SolderedElectronics/Soldered-Inkplate-6-hardware-design/OUTPUTS/V1.2.1/333232.jpg

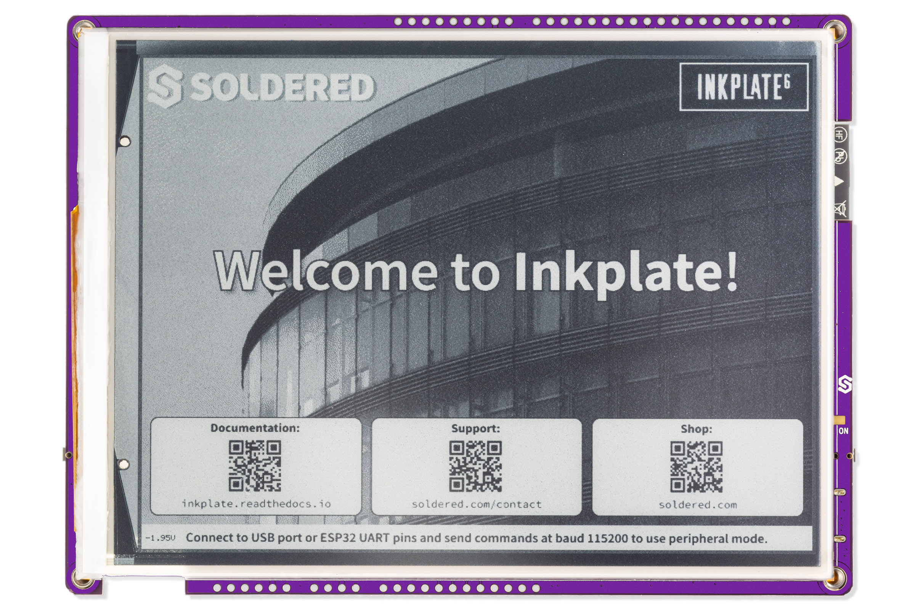
OUTPUTS/V1.2.1/333232.jpg
