SolderedElectronics/Soldered-Inkplate-6-hardware-design/CAD/V1.2.1/CTRL&COMS.kicad_sch

## KiCad design CAD/V1.2.1/CTRL&COMS.kicad_sch (2023-07-25)

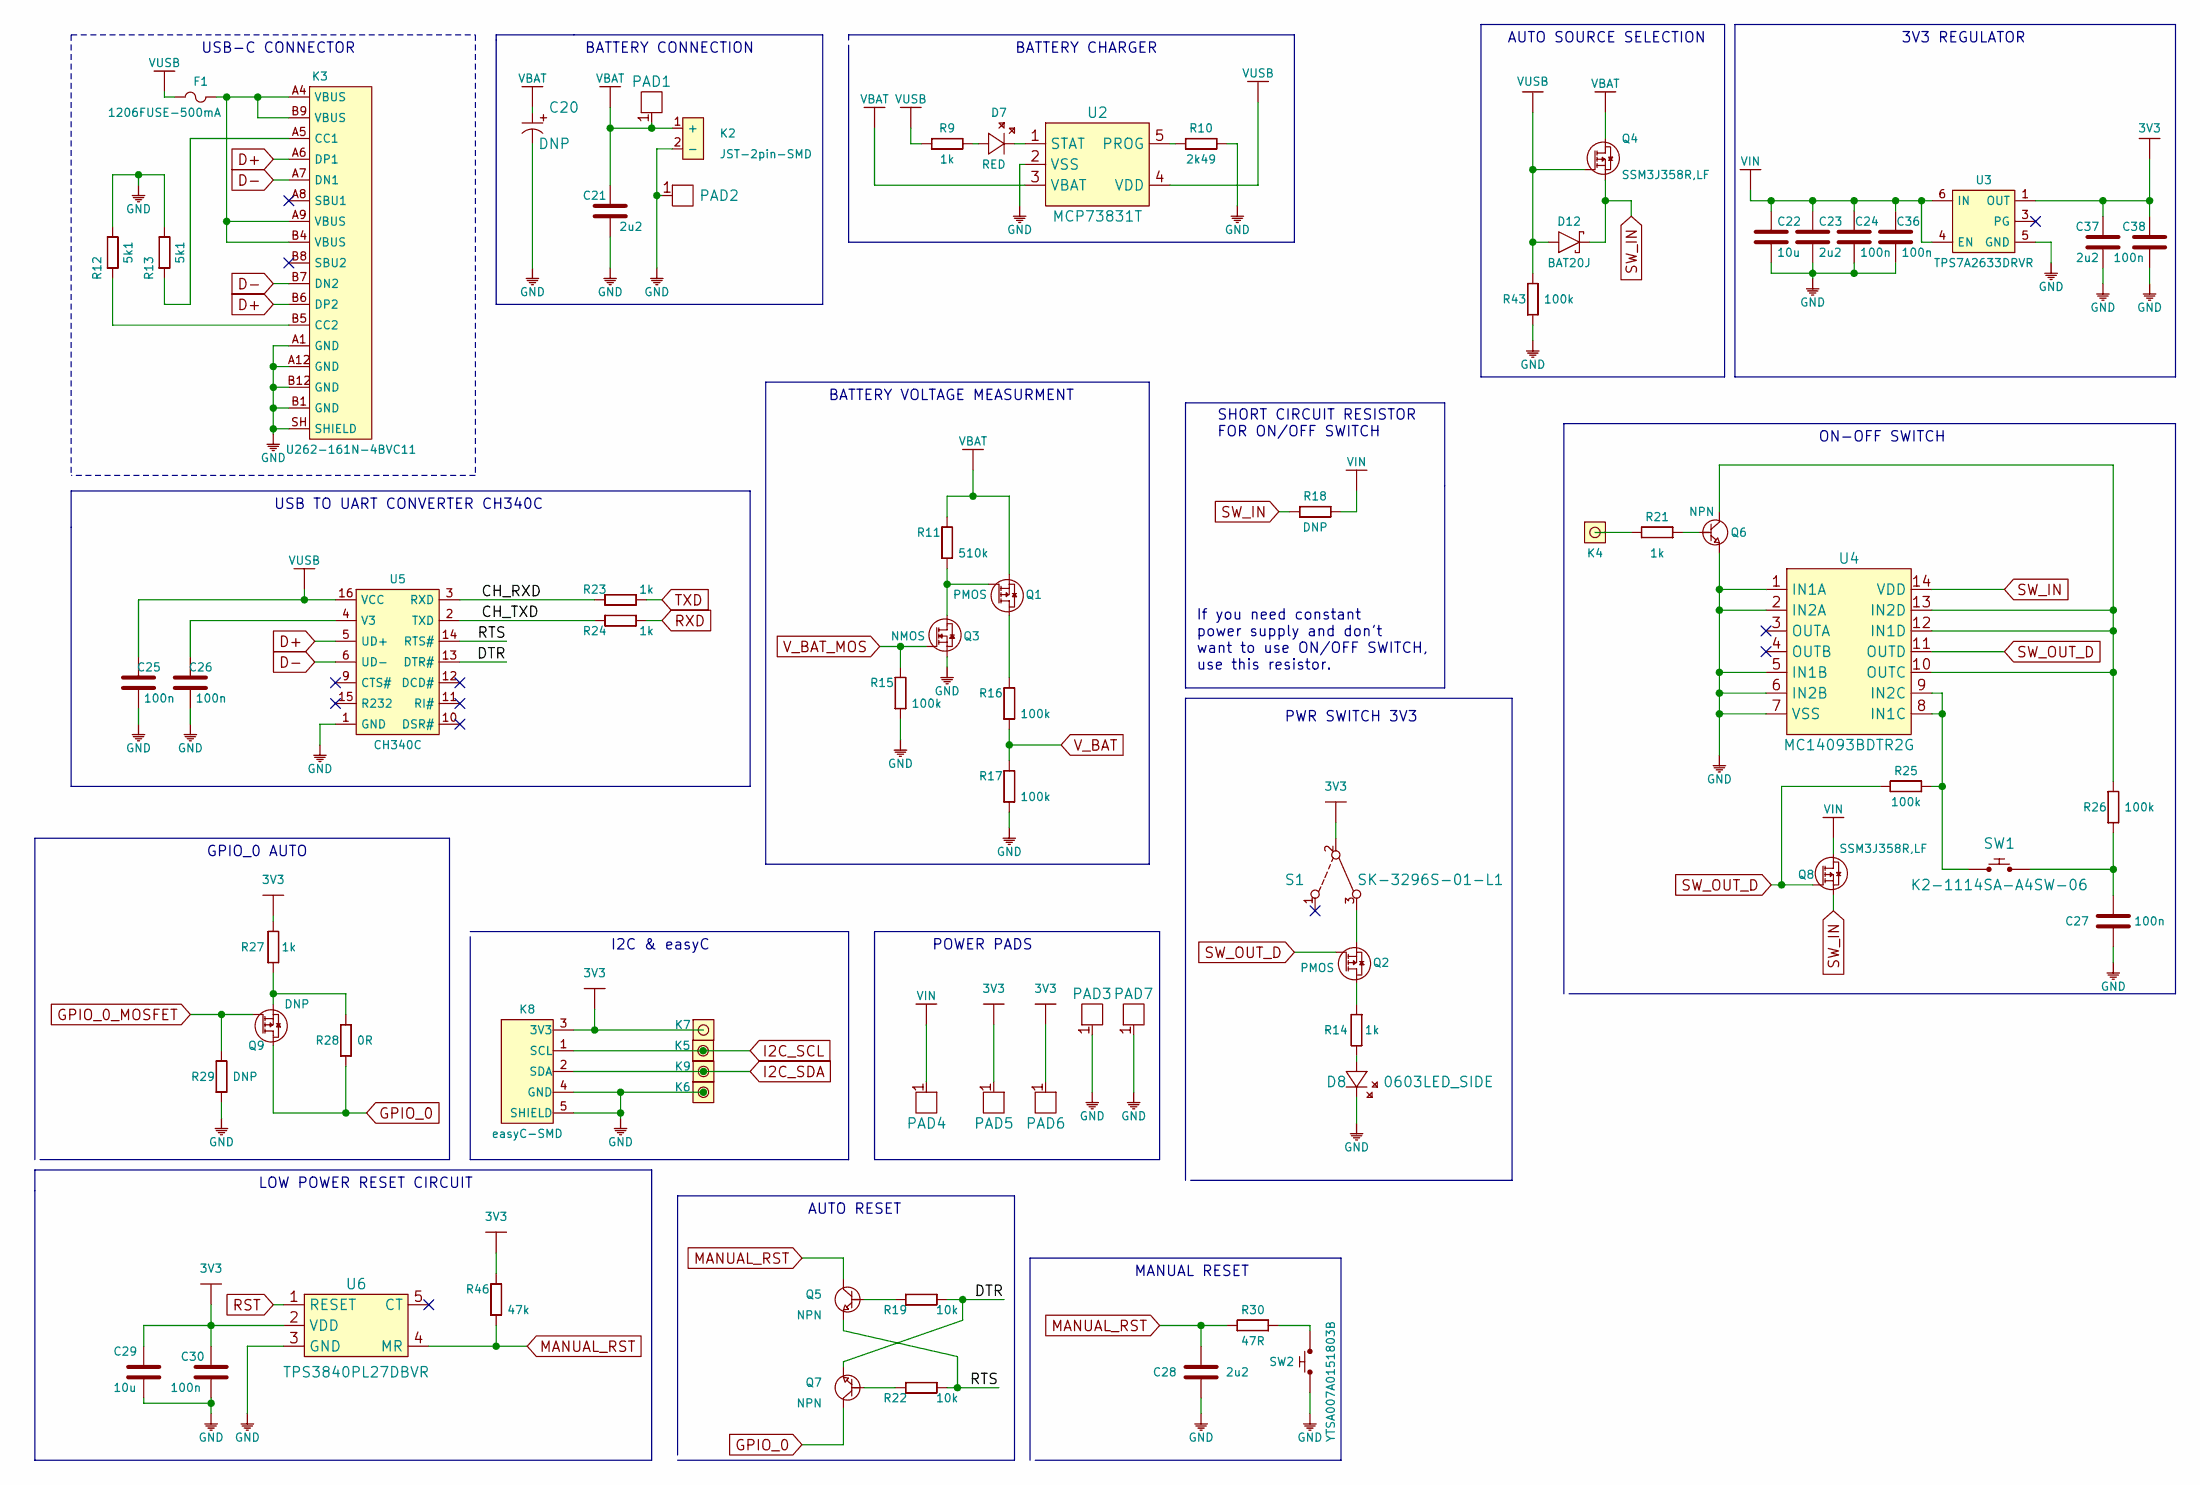
[picture p17: schematic CTRL&COMS.kicad_sch]

Parts:
C20: DNP; 2917C
C21, C23, C28, C37: 2u2; 0603C
C22, C29: 10u; 1206C
C24, C25, C26, C27, C30, C36, C38: 100n; 0603C
D7: RED; 0402LED
D8: 0603LED_SIDE; LTST-S270GKT
D12: BAT20J; SOD-323
F1: 1206FUSE-500mA; 1206FUSE
K2: JST-2pin-SMD
K3: U262-161N-4BVC11
K4, K5, K6, K7, K9: HEADER_MALE_1X1_Inkplate
K8: easyC-SMD; easyC-connector
PAD1, PAD2, PAD3, PAD4, PAD5, PAD6, PAD7: PAD_4x4
Q1, Q2: PMOS; SOT-23-3
Q3: NMOS; SOT-23-3
Q4, Q8: SSM3J358R,LF; SOT-23-3
Q5, Q6, Q7: NPN; SOT-23-3
Q9: DNP; SOT-23-3
R9, R14, R21, R23, R24, R27: 1k; 0603R
R10: 2k49; 0603R
R11: 510k; 0603R
R12, R13: 5k1; 0603R
R15, R16, R17, R25, R26, R43: 100k; 0603R
R18, R29: DNP; 0603R
R19, R22: 10k; 0603R
R28: 0R; 0603R
R30: 47R; 0603R
R46: 47k; 0603R
S1: SK-3296S-01-L1
SW1: K2-1114SA-A4SW-06
SW2: YTSA007A0151803B
U2: MCP73831T; SOT-23-5
U3: TPS7A2633DRVR
U4: MC14093BDTR2G; TSSOP-14
U5: CH340C; SOP-16
U6: TPS3840PL27DBVR; SOT-23-5

Connections:
3V3: C29.2, C30.2, C37.2, C38.2, K7.1, K8.3 (3V3), PAD5.1, PAD6.1, R27.2, R46.2, S1.2, U3.1 (OUT), U6.2 (VDD)
CH_RXD: R23.1, U5.3 (RXD)
CH_TXD: R24.1, U5.2 (TXD)
D+: K3.A6 (DP1), K3.B6 (DP2), U5.5 (UD+)
D-: K3.A7 (DN1), K3.B7 (DN2), U5.6 (UD-)
DTR: Q7.2 (E), R19.2, U5.13 (DTR#)
GND: C20.2 (-), C21.1, C22.1, C23.1, C24.1, C25.1, C26.1, C27.1, C28.1, C29.1, C30.1, C36.1, C37.1, C38.1, D8.2 (K), K2.2 (-), K3.A1 (GND), K3.A12 (GND), K3.B1 (GND), K3.B12 (GND), K3.SH (SHIELD), K6.1, K8.4 (GND), K8.5 (SHIELD), PAD2.1, PAD3.1, PAD7.1, Q3.2 (S), Q6.2 (E), R10.2, R12.2, R13.2, R15.1, R17.1, R29.1, R43.1, SW2.1, U2.2 (VSS), U3.5 (GND), U4.1 (IN1A), U4.2 (IN2A), U4.5 (IN1B), U4.6 (IN2B), U4.7 (VSS), U5.1 (GND), U6.3 (GND)
GPIO_0: Q7.3 (C), Q9.3 (D), R28.1
GPIO_0_MOSFET: Q9.1 (G), R29.2
I2C_SCL: K5.1, K8.1 (SCL)
I2C_SDA: K8.2 (SDA), K9.1
MANUAL_RST: C28.2, Q5.3 (C), R30.2, R46.1, U6.4 (MR)
unnamed: C26.2, U5.4 (V3)
unnamed: C27.2, R26.1, SW1.2
unnamed: D7.1 (A), R9.2
unnamed: D7.2 (K), U2.1 (STAT)
unnamed: D8.1 (A), R14.2
unnamed: F1.2, K3.A4 (VBUS), K3.A9 (VBUS), K3.B4 (VBUS), K3.B9 (VBUS)
unnamed: K3.A5 (CC1), R13.1
unnamed: K3.B5 (CC2), R12.1
unnamed: K4.1, R21.2
unnamed: Q1.1 (G), Q3.3 (D), R11.1
unnamed: Q1.3 (D), R16.2
unnamed: Q2.2 (S), S1.3
unnamed: Q2.3 (D), R14.1
unnamed: Q5.1 (B), R19.1
unnamed: Q6.1 (B), R21.1
unnamed: Q6.3 (C), R26.2, U4.10 (OUTC), U4.12 (IN1D), U4.13 (IN2D)
unnamed: Q7.1 (B), R22.1
unnamed: Q9.2 (S), R27.1, R28.2
unnamed: R10.1, U2.5 (PROG)
unnamed: R25.1, SW1.1, U4.8 (IN1C), U4.9 (IN2C)
unnamed: R30.1, SW2.2
RST: U6.1 (RESET)
RTS: Q5.2 (E), R22.2, U5.14 (RTS#)
RXD: R24.2
SW_IN: D12.2 (C), Q4.2 (S), Q8.2 (S), R18.1, U4.14 (VDD)
SW_OUT_D: Q2.1 (G), Q8.1 (G), R25.2, U4.11 (OUTD)
TXD: R23.2
VBAT: C20.1 (+), C21.2, K2.1 (+), PAD1.1, Q1.2 (S), Q4.3 (D), R11.2, U2.3 (VBAT)
VIN: C22.2, C23.2, C24.2, C36.2, PAD4.1, Q8.3 (D), R18.2, U3.4 (EN), U3.6 (IN)
VUSB: C25.2, D12.1 (A), F1.1, Q4.1 (G), R9.1, R43.2, U2.4 (VDD), U5.16 (VCC)
V_BAT: R16.1, R17.2
V_BAT_MOS: Q3.1 (G), R15.2

Notes on the sheet:
PWR SWITCH 3V3
BATTERY VOLTAGE MEASURMENT
AUTO RESET
GPIO_0 AUTO
BATTERY CHARGER
SHORT CIRCUIT RESISTOR FOR ON/OFF SWITCH
If you need constant power supply and don't want to use ON/OFF SWITCH, use this resistor.
POWER PADS
LOW POWER RESET CIRCUIT
MANUAL RESET
AUTO SOURCE SELECTION
BATTERY CONNECTION
3V3 REGULATOR
USB TO UART CONVERTER CH340C
ON-OFF SWITCH
USB-C CONNECTOR
I2C & easyC
