SolderedElectronics/Soldered-Inkplate-6-hardware-design/CAD/V1.2.1/Connector.kicad_sch

## KiCad design CAD/V1.2.1/Connector.kicad_sch (2023-07-25)

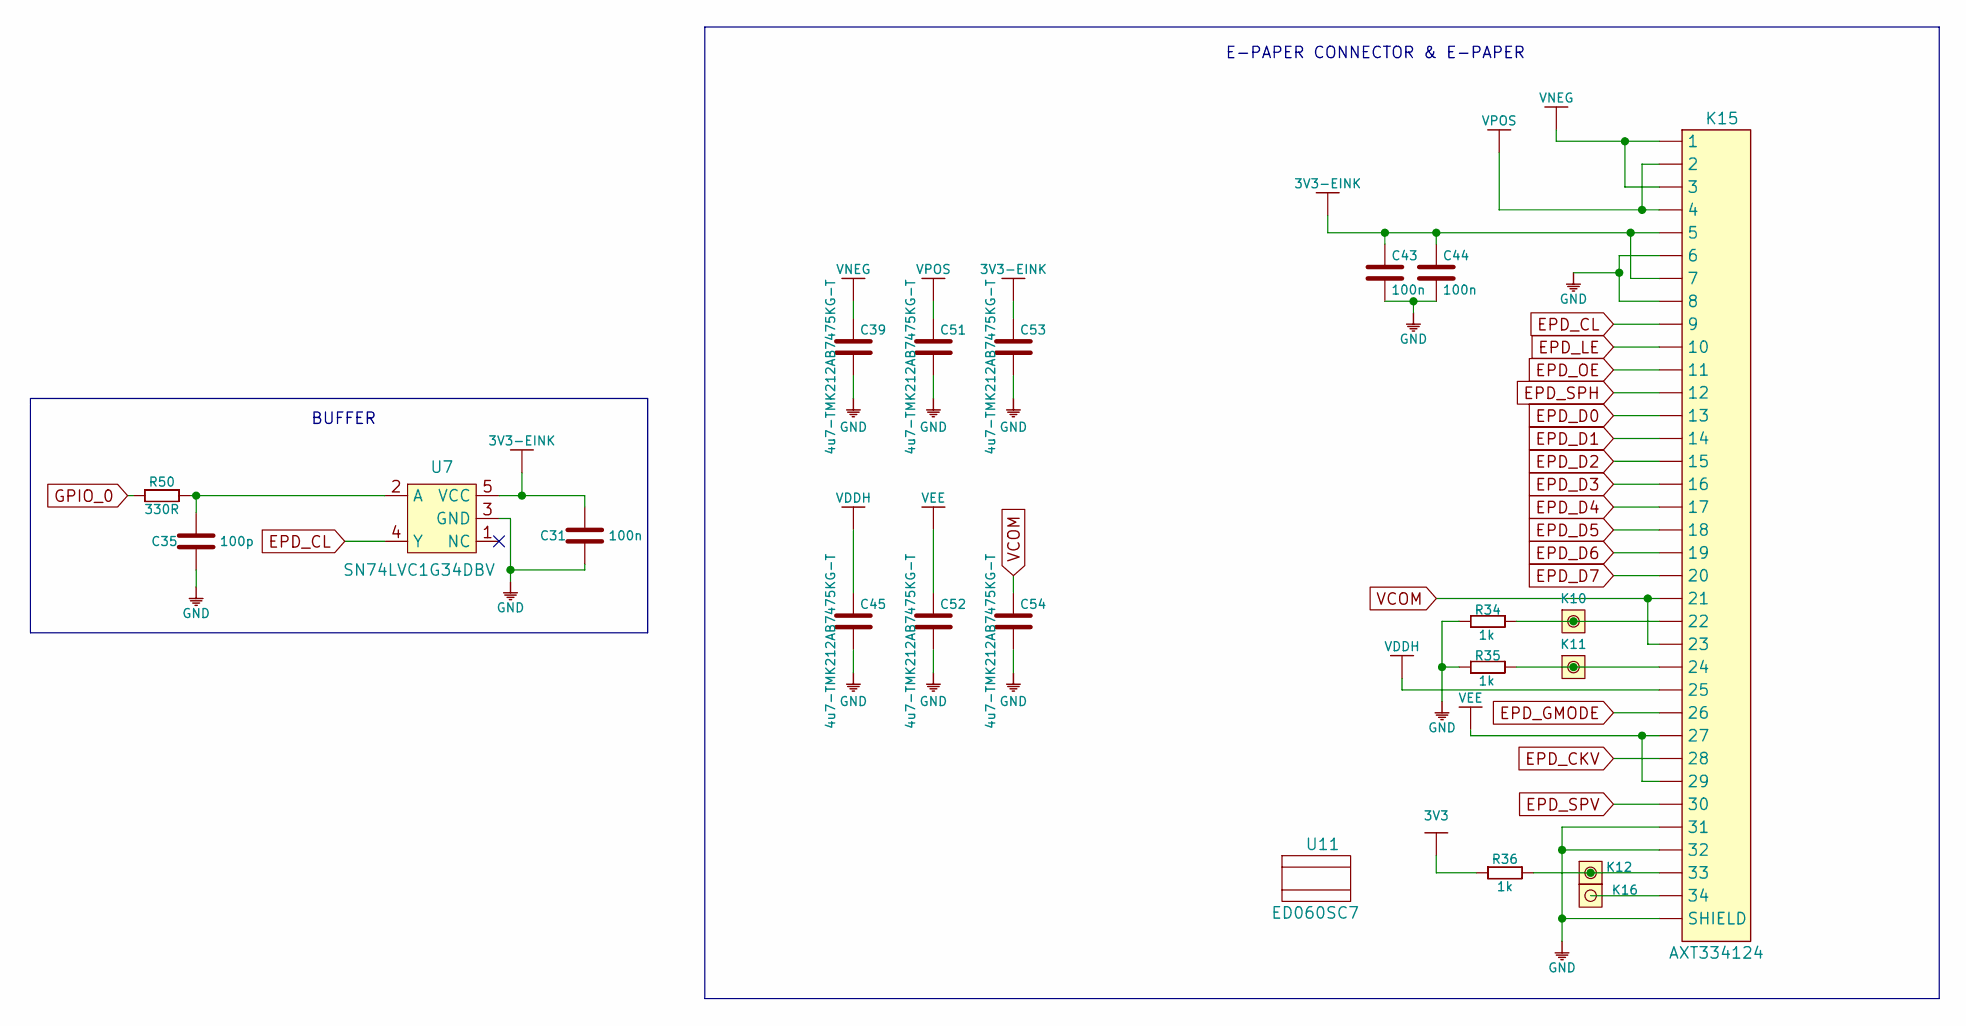
[picture p18: schematic Connector.kicad_sch]

Parts:
C31, C43, C44: 100n; 0603C
C35: 100p; 0603C
C39, C45, C51, C52, C53, C54: 4u7-TMK212AB7475KG-T; 0805C
K10, K11, K12, K16: HEADER_MALE_1X1_Inkplate
K15: AXT334124
R34, R35, R36: 1k; 0603R
R50: 330R; 0603R
U7: SN74LVC1G34DBV
U11: ED060SC7

Connections:
3V3: R36.1
3V3-EINK: C31.2, C43.2, C44.2, C53.2, K15.5, K15.7, U7.5 (VCC)
EPD_CKV: K15.28
EPD_CL: K15.9, U7.4 (Y)
EPD_D0: K15.13
EPD_D1: K15.14
EPD_D2: K15.15
EPD_D3: K15.16
EPD_D4: K15.17
EPD_D5: K15.18
EPD_D6: K15.19
EPD_D7: K15.20
EPD_GMODE: K15.26
EPD_LE: K15.10
EPD_OE: K15.11
EPD_SPH: K15.12
EPD_SPV: K15.30
GND: C31.1, C35.1, C39.1, C43.1, C44.1, C45.1, C51.1, C52.1, C53.1, C54.1, K15.6, K15.8, K15.31, K15.32, K15.SH (SHIELD), R34.1, R35.1, U7.3 (GND)
GPIO_0: R50.1
unnamed: C35.2, R50.2, U7.2 (A)
unnamed: K10.1, K15.22, R34.2
unnamed: K11.1, K15.24, R35.2
unnamed: K12.1, K15.33, R36.2
unnamed: K15.34, K16.1
VCOM: C54.2, K15.21, K15.23
VDDH: C45.2, K15.25
VEE: C52.2, K15.27, K15.29
VNEG: C39.2, K15.1, K15.3
VPOS: C51.2, K15.2, K15.4

Notes on the sheet:
E-PAPER CONNECTOR & E-PAPER
BUFFER
