SolderedElectronics/Soldered-Inkplate-6-hardware-design/CAD/V1.2.1/MCU.kicad_sch

## KiCad design CAD/V1.2.1/MCU.kicad_sch (2023-07-25)

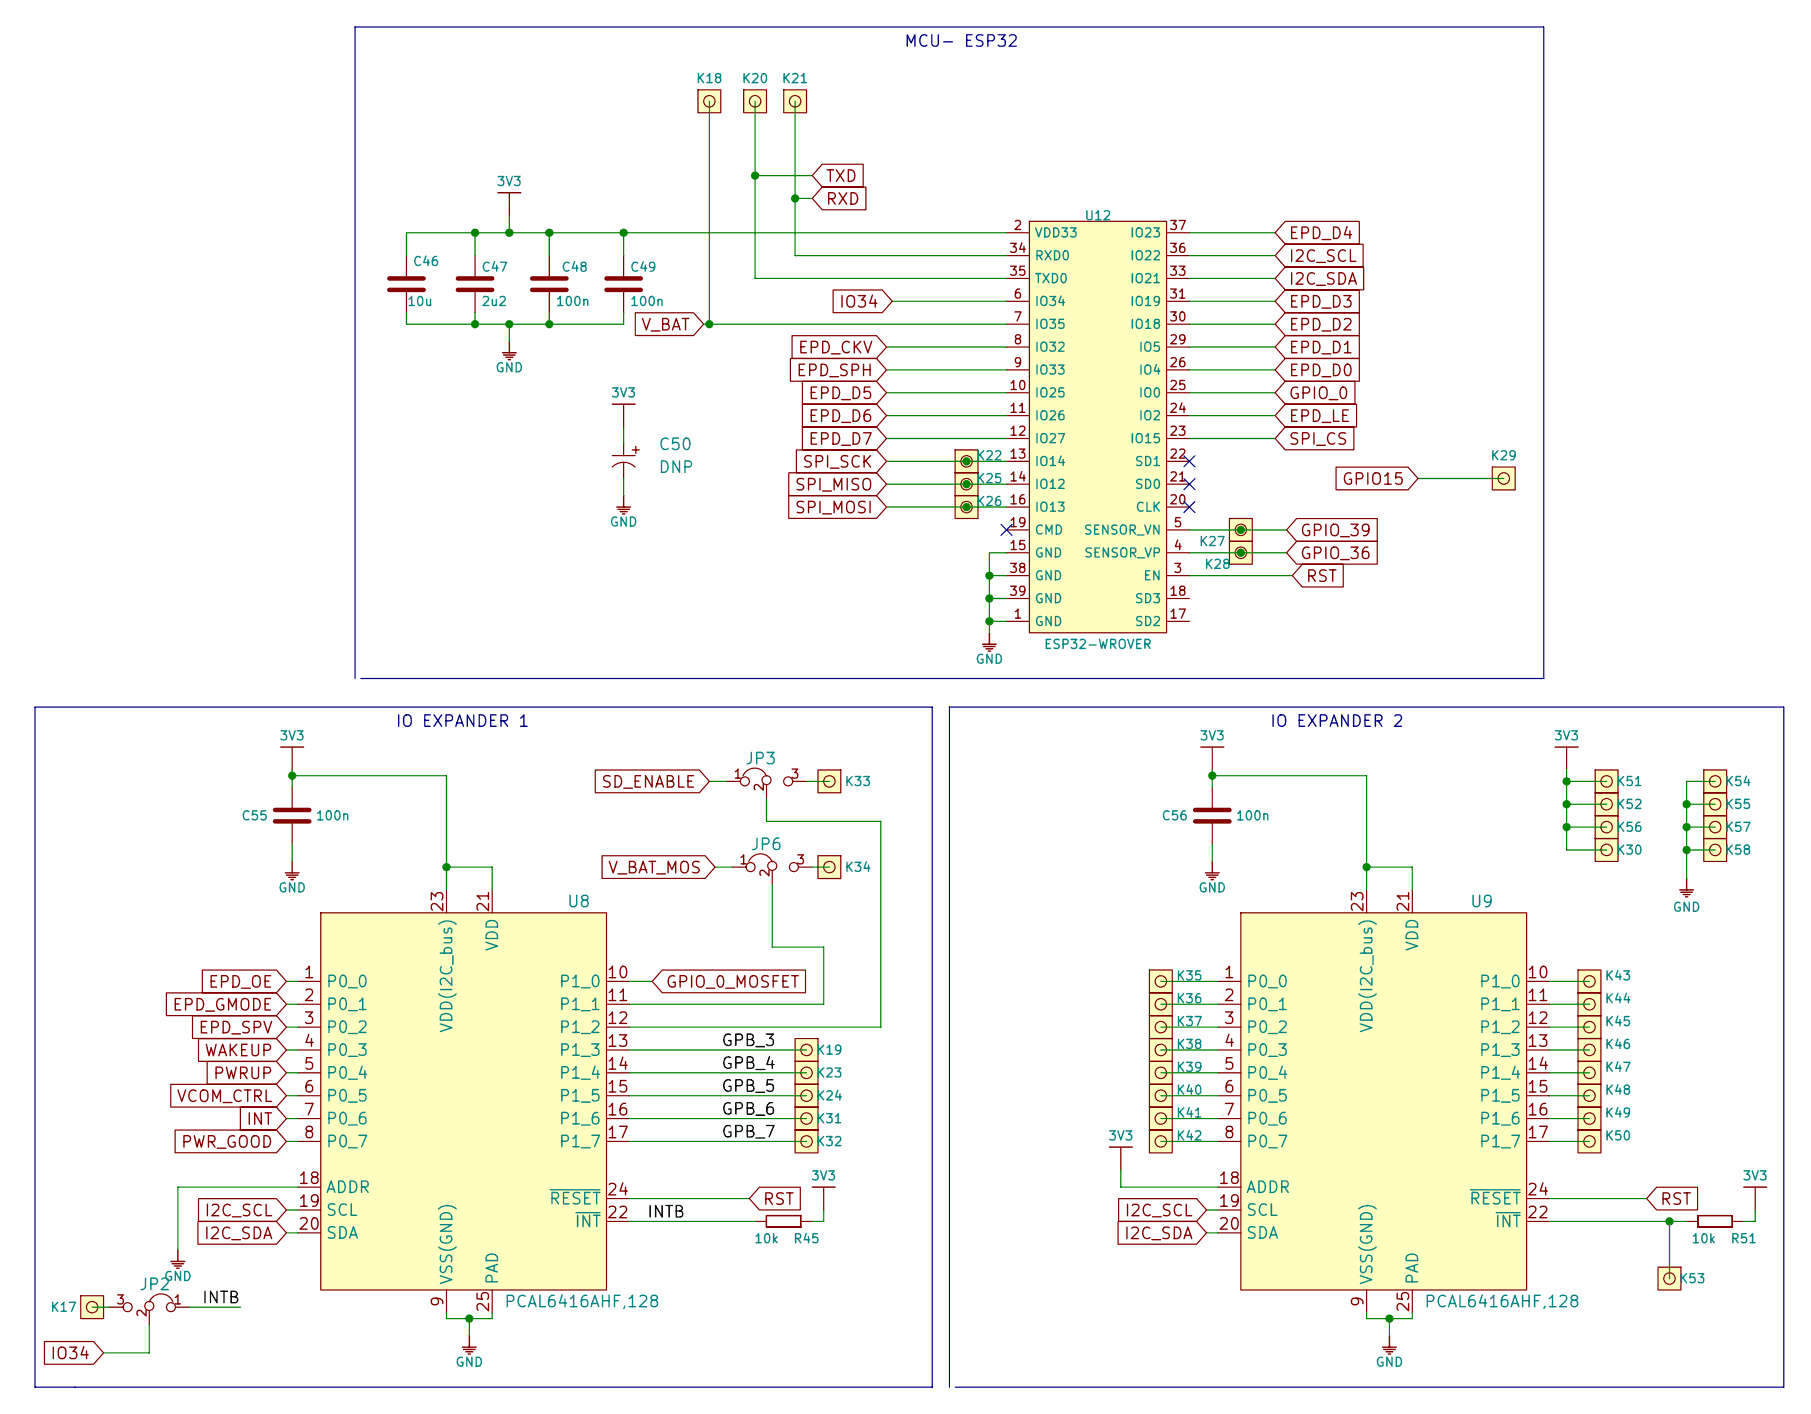
[picture p19: schematic MCU.kicad_sch]

Parts:
C46: 10u; 1206C
C47: 2u2; 0603C
C48, C49, C55, C56: 100n; 0603C
C50: DNP; 2917C
JP2, JP3, JP6: SMD_JUMPER_3_PAD_CONNECTED_LEFT_TRACE
K17, K18, K19, K20, K21, K22, K23, K24, K25, K26, K27, K28, K29, K30, K31, K32, K33, K34, K35, K36, K37, K38, K39, K40, K41, K42, K43, K44, K45, K46, K47, K48, K49, K50, K51, K52, K53, K54, K55, K56, K57, K58: HEADER_MALE_1X1_Inkplate
R45, R51: 10k; 0603R
U8, U9: PCAL6416AHF,128
U12: ESP32-WROVER

Connections:
3V3: C46.2, C47.2, C48.2, C49.2, C50.1 (+), C55.2, C56.2, K30.1, K51.1, K52.1, K56.1, R45.1, R51.1, U8.21 (VDD), U8.23 (VDD(I2C_bus)), U9.18 (ADDR), U9.21 (VDD), U9.23 (VDD(I2C_bus)), U12.2 (VDD33)
EPD_CKV: U12.8 (IO32)
EPD_D0: U12.26 (IO4)
EPD_D1: U12.29 (IO5)
EPD_D2: U12.30 (IO18)
EPD_D3: U12.31 (IO19)
EPD_D4: U12.37 (IO23)
EPD_D5: U12.10 (IO25)
EPD_D6: U12.11 (IO26)
EPD_D7: U12.12 (IO27)
EPD_GMODE: U8.2 (P0_1)
EPD_LE: U12.24 (IO2)
EPD_OE: U8.1 (P0_0)
EPD_SPH: U12.9 (IO33)
EPD_SPV: U8.3 (P0_2)
GND: C46.1, C47.1, C48.1, C49.1, C50.2 (-), C55.1, C56.1, K54.1, K55.1, K57.1, K58.1, U8.9 (VSS(GND)), U8.18 (ADDR), U8.25 (PAD), U9.9 (VSS(GND)), U9.25 (PAD), U12.1 (GND), U12.15 (GND), U12.38 (GND), U12.39 (GND)
GPB_3: K19.1, U8.13 (P1_3)
GPB_4: K23.1, U8.14 (P1_4)
GPB_5: K24.1, U8.15 (P1_5)
GPB_6: K31.1, U8.16 (P1_6)
GPB_7: K32.1, U8.17 (P1_7)
GPIO15: K29.1
GPIO_0: U12.25 (IO0)
GPIO_0_MOSFET: U8.10 (P1_0)
GPIO_36: K28.1, U12.4 (SENSOR_VP)
GPIO_39: K27.1, U12.5 (SENSOR_VN)
I2C_SCL: U8.19 (SCL), U9.19 (SCL), U12.36 (IO22)
I2C_SDA: U8.20 (SDA), U9.20 (SDA), U12.33 (IO21)
INT: U8.7 (P0_6)
INTB: JP2.1, R45.2, U8.22 (~INT)
IO34: JP2.2, U12.6 (IO34)
unnamed: JP2.3, K17.1
unnamed: JP3.2, U8.12 (P1_2)
unnamed: JP3.3, K33.1
unnamed: JP6.2, U8.11 (P1_1)
unnamed: JP6.3, K34.1
unnamed: K35.1, U9.1 (P0_0)
unnamed: K36.1, U9.2 (P0_1)
unnamed: K37.1, U9.3 (P0_2)
unnamed: K38.1, U9.4 (P0_3)
unnamed: K39.1, U9.5 (P0_4)
unnamed: K40.1, U9.6 (P0_5)
unnamed: K41.1, U9.7 (P0_6)
unnamed: K42.1, U9.8 (P0_7)
unnamed: K43.1, U9.10 (P1_0)
unnamed: K44.1, U9.11 (P1_1)
unnamed: K45.1, U9.12 (P1_2)
unnamed: K46.1, U9.13 (P1_3)
unnamed: K47.1, U9.14 (P1_4)
unnamed: K48.1, U9.15 (P1_5)
unnamed: K49.1, U9.16 (P1_6)
unnamed: K50.1, U9.17 (P1_7)
unnamed: K53.1, R51.2, U9.22 (~INT)
PWRUP: U8.5 (P0_4)
PWR_GOOD: U8.8 (P0_7)
RST: U8.24 (~RESET), U9.24 (~RESET), U12.3 (EN)
RXD: K21.1, U12.34 (RXD0)
SD_ENABLE: JP3.1
SPI_CS: U12.23 (IO15)
SPI_MISO: K25.1, U12.14 (IO12)
SPI_MOSI: K26.1, U12.16 (IO13)
SPI_SCK: K22.1, U12.13 (IO14)
TXD: K20.1, U12.35 (TXD0)
VCOM_CTRL: U8.6 (P0_5)
V_BAT: K18.1, U12.7 (IO35)
V_BAT_MOS: JP6.1
WAKEUP: U8.4 (P0_3)

Notes on the sheet:
MCU- ESP32
IO EXPANDER 2
IO EXPANDER 1
