SolderedElectronics/Soldered-Inkplate-6-hardware-design/CAD/V1.2.1/POWER.kicad_sch

## KiCad design CAD/V1.2.1/POWER.kicad_sch (2023-07-25)

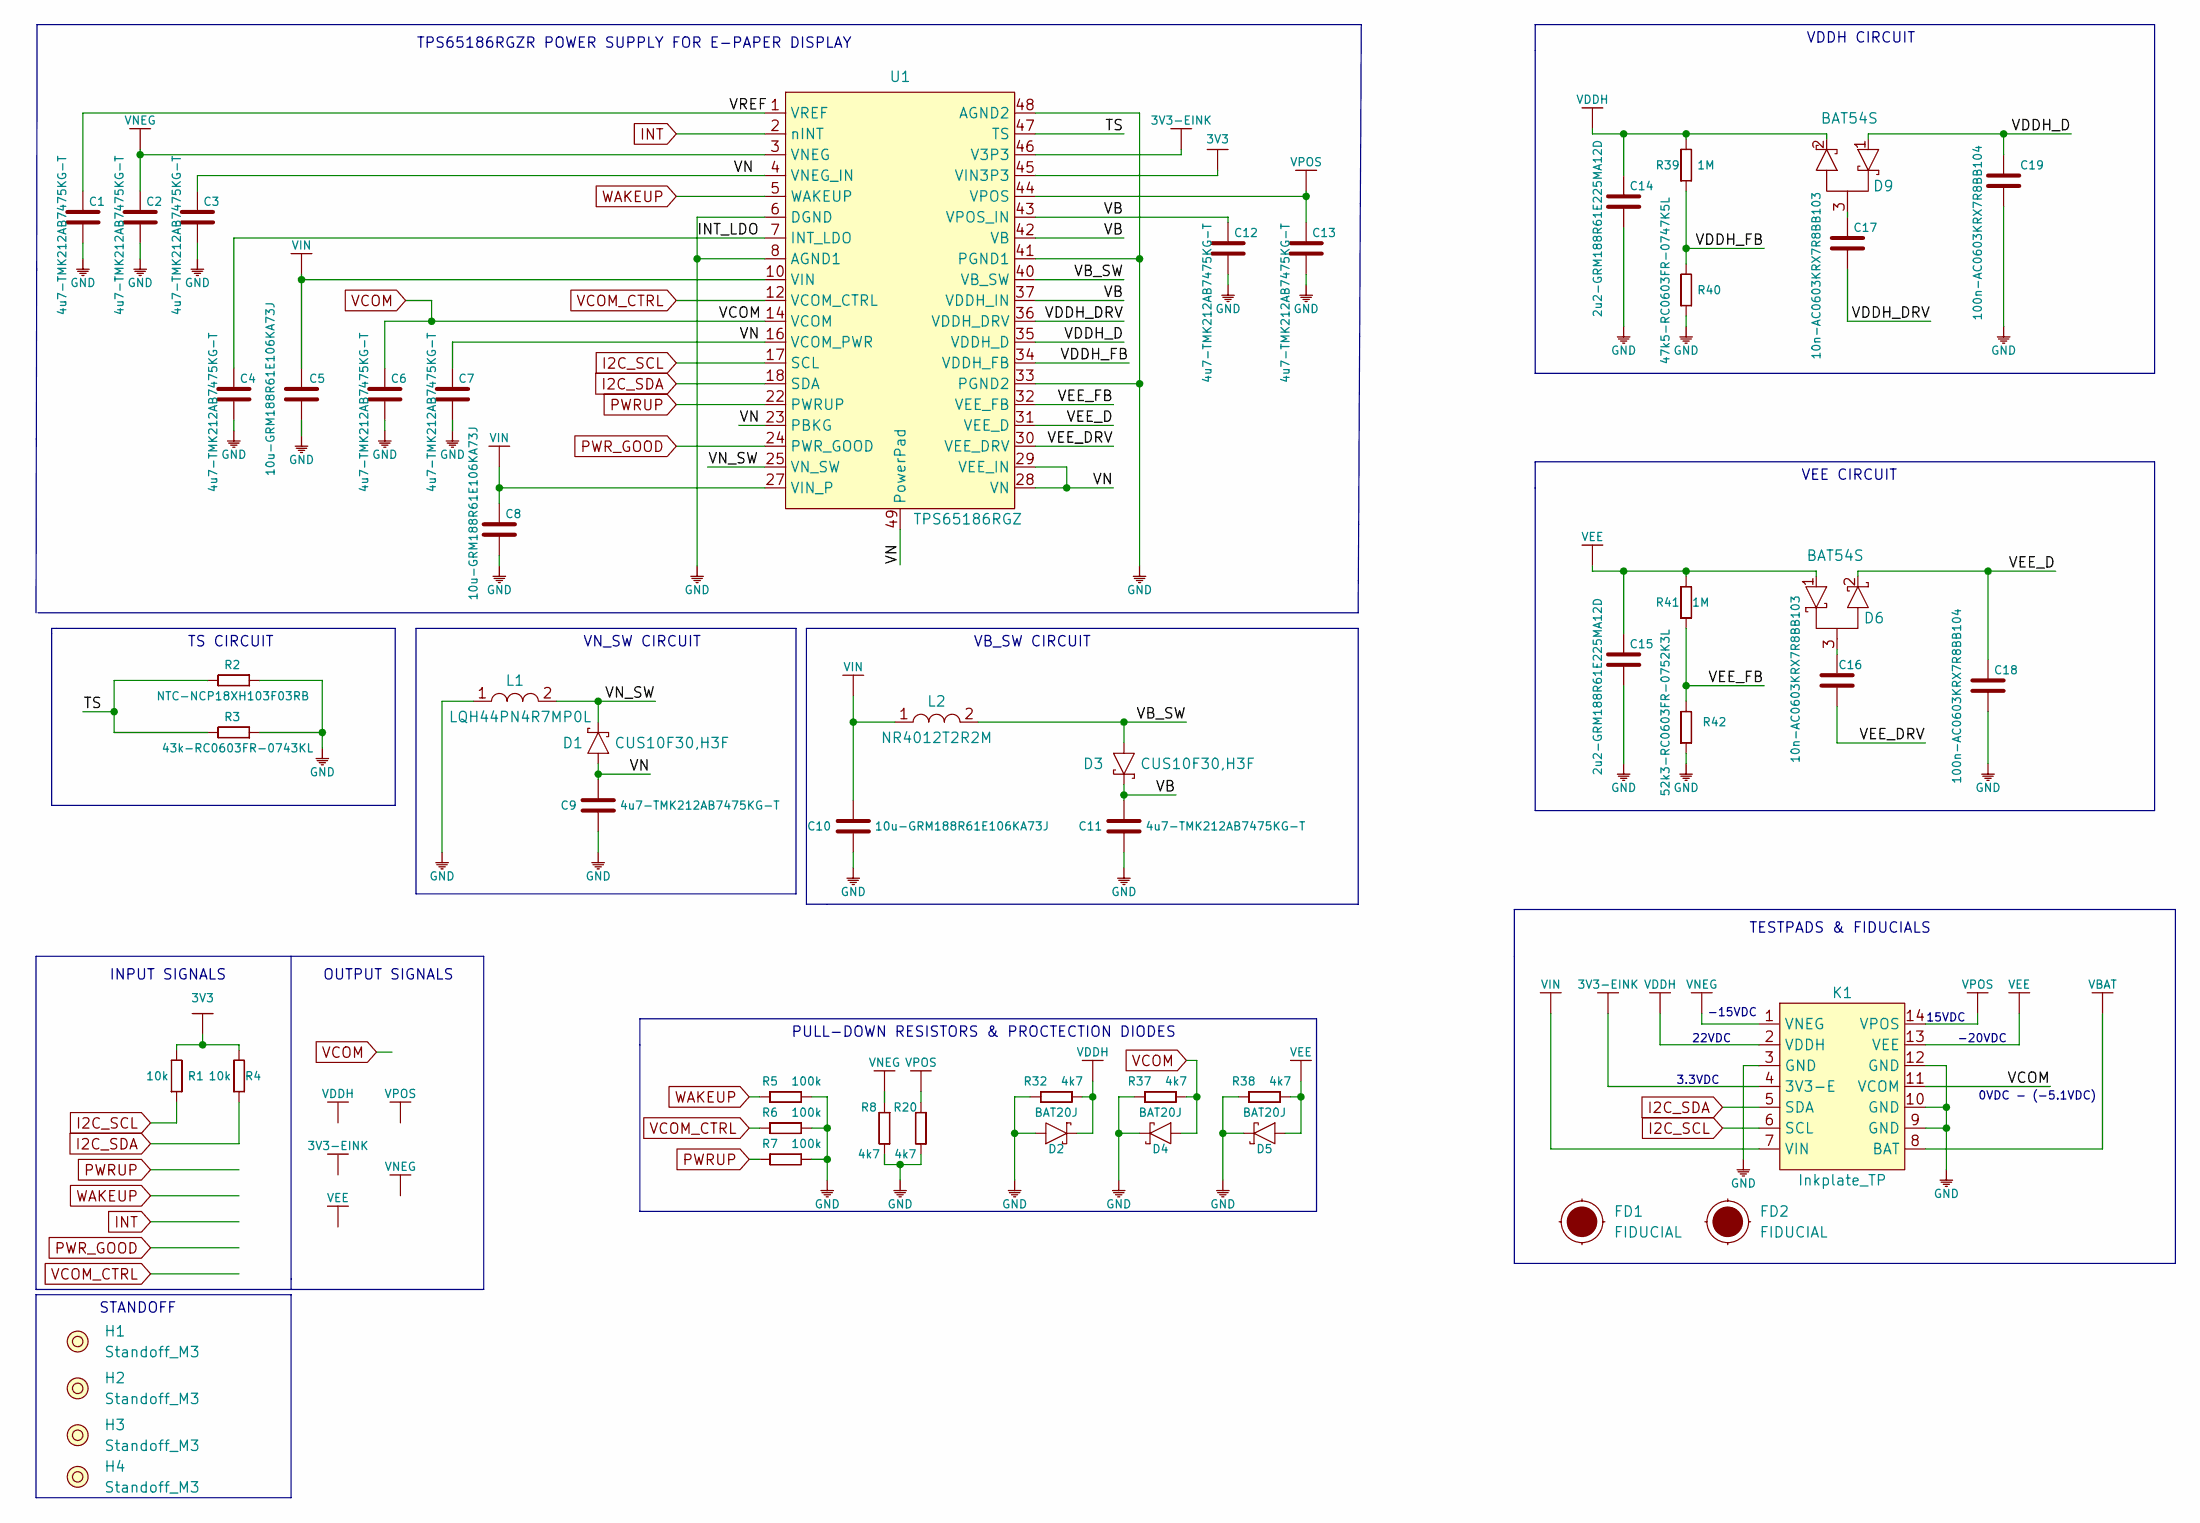
[picture p20: schematic POWER.kicad_sch]

Parts:
C1, C2, C3, C4, C6, C7, C9, C11, C12, C13: 4u7-TMK212AB7475KG-T; 0805C
C5, C8, C10: 10u-GRM188R61E106KA73J; 0603C
C14, C15: 2u2-GRM188R61E225MA12D; 0603C
C16, C17: 10n-AC0603KRX7R8BB103; 0603C
C18, C19: 100n-AC0603KRX7R8BB104; 0603C
D1, D3: CUS10F30,H3F; SOD-323-2
D2, D4, D5: BAT20J; SOD-323
D6, D9: BAT54S; SOT-23-3
FD1, FD2: FIDUCIAL; FIDUCIAL_23
H1, H2, H3, H4: Standoff_M3
K1: Inkplate_TP; INKPLATE TEST HEADER
L1: LQH44PN4R7MP0L; 1515L
L2: NR4012T2R2M; NR4012
R1, R4: 10k; 0603R
R2: NTC-NCP18XH103F03RB; 0603R
R3: 43k-RC0603FR-0743KL; 0603R
R5, R6, R7: 100k; 0603R
R8, R20, R32, R37, R38: 4k7; 0603R
R39, R41: 1M; 0603R
R40: 47k5-RC0603FR-0747K5L; 0603R
R42: 52k3-RC0603FR-0752K3L; 0603R
U1: TPS65186RGZ; VQFN-49

Connections:
3V3: R1.2, R4.2, U1.45 (VIN3P3)
3V3-EINK: K1.4 (3V3-E), U1.46 (V3P3)
GND: C1.1, C2.1, C3.1, C4.1, C5.1, C6.1, C7.1, C8.1, C9.2, C10.1, C11.2, C12.1, C13.1, C14.1, C15.1, C18.1, C19.1, D2.1 (A), D4.2 (C), D5.2 (C), K1.3 (GND), K1.9 (GND), K1.10 (GND), K1.12 (GND), L1.1, R2.1, R3.1, R5.2, R6.2, R7.2, R8.2, R20.2, R32.1, R37.1, R38.1, R40.1, R42.1, U1.6 (DGND), U1.8 (AGND1), U1.33 (PGND2), U1.41 (PGND1), U1.48 (AGND2)
I2C_SCL: K1.6 (SCL), R1.1, U1.17 (SCL)
I2C_SDA: K1.5 (SDA), R4.1, U1.18 (SDA)
INT: U1.2 (nINT)
INT_LDO: C4.2, U1.7 (INT_LDO)
unnamed: C16.1, D6.3
unnamed: C17.2, D9.3
PWRUP: R7.1, U1.22 (PWRUP)
PWR_GOOD: U1.24 (PWR_GOOD)
TS: R2.2, R3.2, U1.47 (TS)
VB: C11.1, C12.2, D3.1 (C), U1.37 (VDDH_IN), U1.42 (VB), U1.43 (VPOS_IN)
VBAT: K1.8 (BAT)
VB_SW: D3.2 (A), L2.2, U1.40 (VB_SW)
VCOM: C6.2, D4.1 (A), K1.11 (VCOM), R37.2, U1.14 (VCOM)
VCOM_CTRL: R6.1, U1.12 (VCOM_CTRL)
VDDH: C14.2, D2.2 (C), D9.2 (K), K1.2 (VDDH), R32.2, R39.2
VDDH_D: C19.2, D9.1 (A), U1.35 (VDDH_D)
VDDH_DRV: C17.1, U1.36 (VDDH_DRV)
VDDH_FB: R39.1, R40.2, U1.34 (VDDH_FB)
VEE: C15.2, D5.1 (A), D6.1 (A), K1.13 (VEE), R38.2, R41.2
VEE_D: C18.2, D6.2 (K), U1.31 (VEE_D)
VEE_DRV: C16.2, U1.30 (VEE_DRV)
VEE_FB: R41.1, R42.2, U1.32 (VEE_FB)
VIN: C5.2, C8.2, C10.2, K1.7 (VIN), L2.1, U1.10 (VIN), U1.27 (VIN_P)
VN: C3.2, C7.2, C9.1, D1.2 (A), U1.4 (VNEG_IN), U1.16 (VCOM_PWR), U1.23 (PBKG), U1.28 (VN), U1.29 (VEE_IN), U1.49 (PowerPad)
VNEG: C2.2, K1.1 (VNEG), R8.1, U1.3 (VNEG)
VN_SW: D1.1 (C), L1.2, U1.25 (VN_SW)
VPOS: C13.2, K1.14 (VPOS), R20.1, U1.44 (VPOS)
VREF: C1.2, U1.1 (VREF)
WAKEUP: R5.1, U1.5 (WAKEUP)

Notes on the sheet:
3.3VDC
OUTPUT SIGNALS
VEE CIRCUIT
STANDOFF
-15VDC
VB_SW CIRCUIT
VDDH CIRCUIT
TESTPADS & FIDUCIALS
0VDC - (-5.1VDC)
PULL-DOWN RESISTORS & PROCTECTION DIODES
TS CIRCUIT
VN_SW CIRCUIT
22VDC
TPS65186RGZR POWER SUPPLY FOR E-PAPER DISPLAY
INPUT SIGNALS
-20VDC
15VDC
