SolderedElectronics/Soldered-Inkplate-6-hardware-design/CAD/V1.2.1/SD_RTC_GPIO.kicad_sch

## KiCad design CAD/V1.2.1/SD_RTC_GPIO.kicad_sch (2023-07-25)

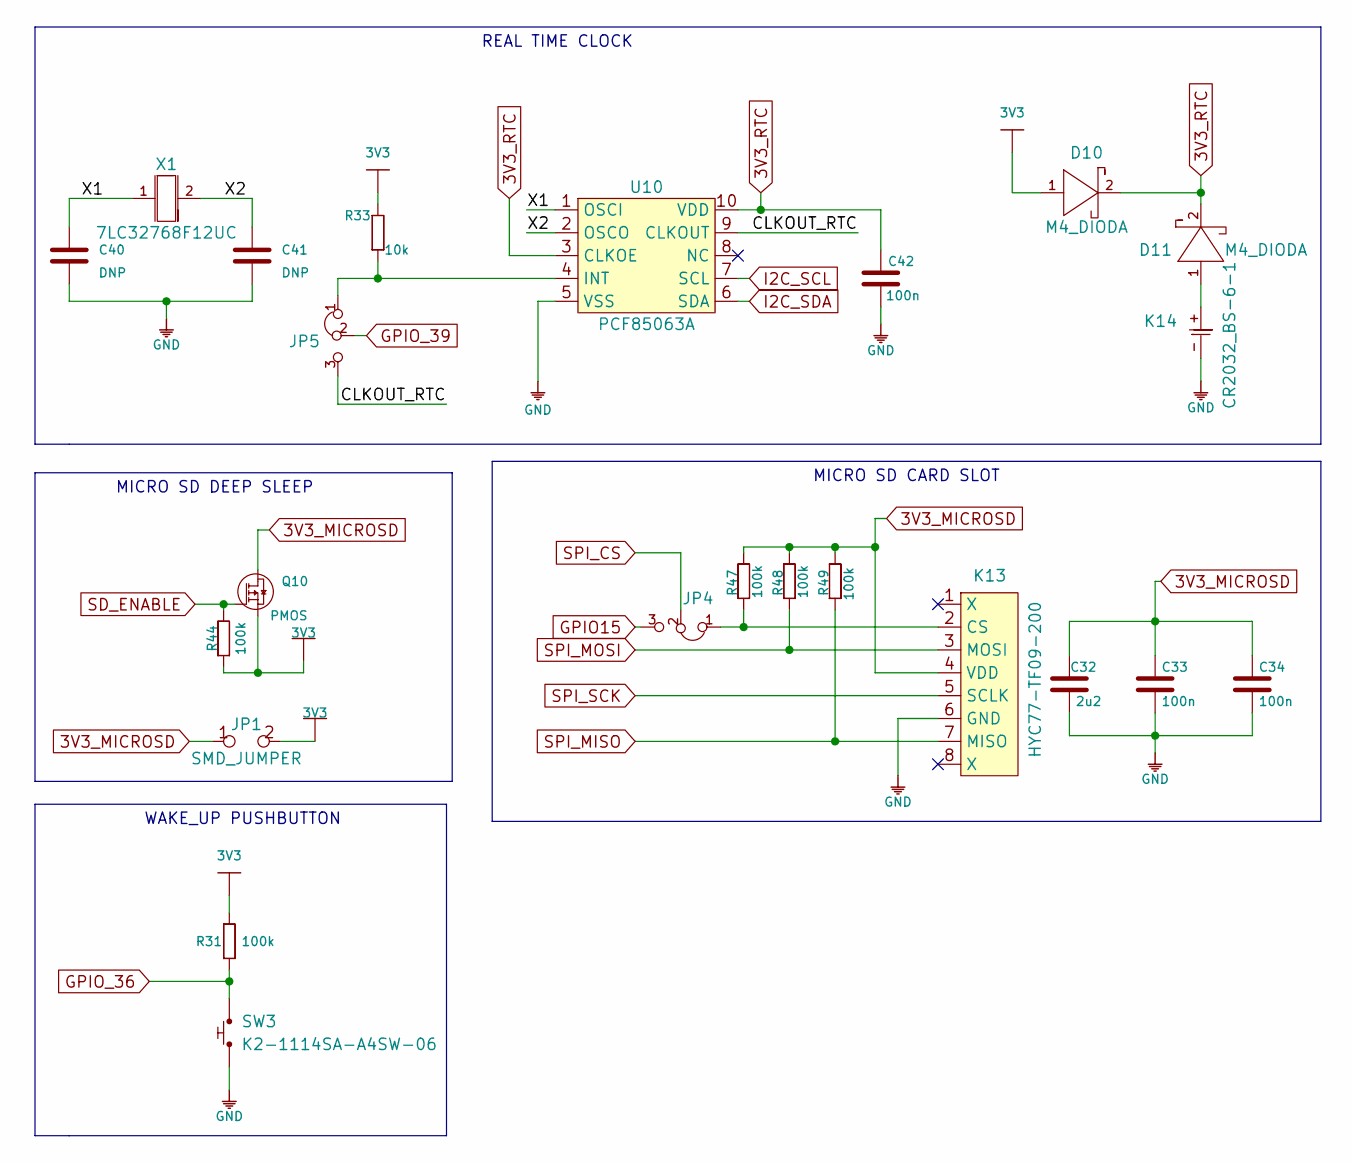
[picture p21: schematic SD_RTC_GPIO.kicad_sch]

Parts:
C32: 2u2; 0603C
C33, C34, C42: 100n; 0603C
C40, C41: DNP; 0603C
D10, D11: M4_DIODA
JP1: SMD_JUMPER
JP4, JP5: SMD_JUMPER_3_PAD_CONNECTED_LEFT_TRACE
K13: HYC77-TF09-200
K14: CR2032_BS-6-1; CR2032-BS-6-1
Q10: PMOS; SOT-23-3
R31, R44, R47, R48, R49: 100k; 0603R
R33: 10k; 0603R
SW3: K2-1114SA-A4SW-06
U10: PCF85063A
X1: 7LC32768F12UC; ABS07AIG-32.768KHZ-7-D-T

Connections:
3V3: D10.1 (A), JP1.2, Q10.2 (S), R31.2, R33.2, R44.1
3V3_MICROSD: C32.2, C33.2, C34.2, JP1.1, K13.4 (VDD), Q10.3 (D), R47.2, R48.2, R49.2
3V3_RTC: C42.2, D10.2 (K), D11.2 (K), U10.3 (CLKOE), U10.10 (VDD)
CLKOUT_RTC: JP5.3, U10.9 (CLKOUT)
GND: C32.1, C33.1, C34.1, C40.1, C41.1, C42.1, K13.6 (GND), K14.-, SW3.1, U10.5 (VSS)
GPIO15: JP4.3
GPIO_36: R31.1, SW3.2
GPIO_39: JP5.2
I2C_SCL: U10.7 (SCL)
I2C_SDA: U10.6 (SDA)
unnamed: D11.1 (A), K14.+
unnamed: JP4.1, K13.2 (CS), R47.1
unnamed: JP5.1, R33.1, U10.4 (INT)
SD_ENABLE: Q10.1 (G), R44.2
SPI_CS: JP4.2
SPI_MISO: K13.7 (MISO), R49.1
SPI_MOSI: K13.3 (MOSI), R48.1
SPI_SCK: K13.5 (SCLK)
X1: C40.2, U10.1 (OSCI), X1.1
X2: C41.2, U10.2 (OSCO), X1.2

Notes on the sheet:
MICRO SD CARD SLOT
REAL TIME CLOCK
MICRO SD DEEP SLEEP
WAKE_UP PUSHBUTTON
